christermj/bachelor-2026-3d-printing-underwater-prototyping/figurer/ekstra/20260315_124856.jpg

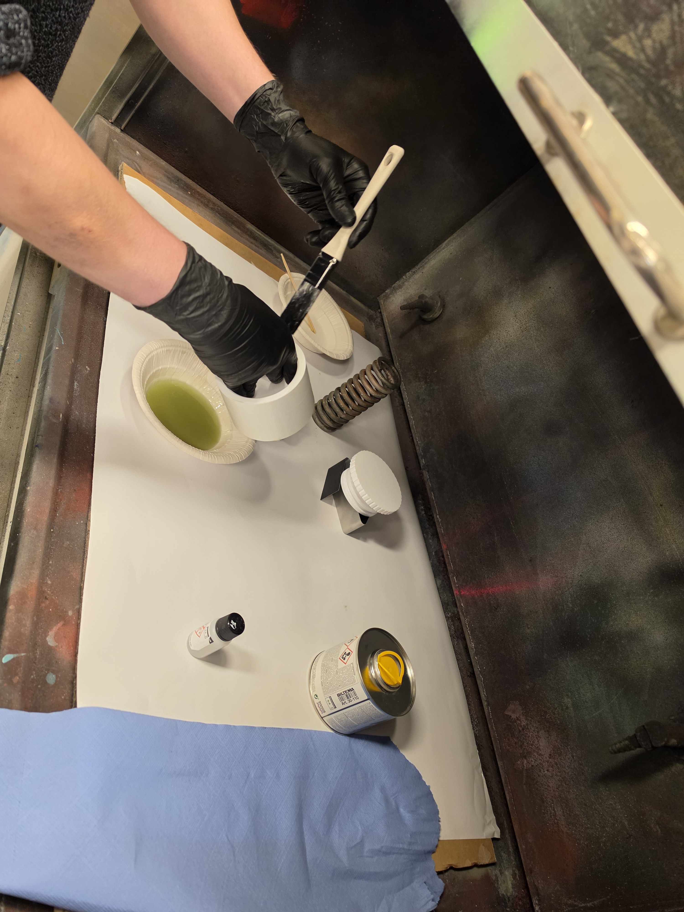
figurer/ekstra/20260315_124856.jpg
