christermj/bachelor-2026-3d-printing-underwater-prototyping/figurer/ekstra/IMG20260116104449.jpg

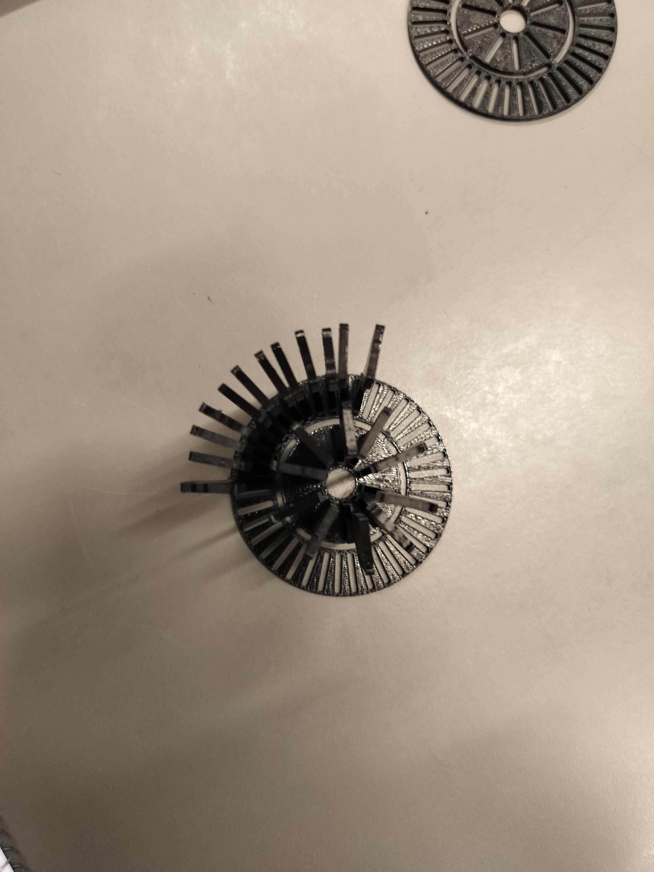
figurer/ekstra/IMG20260116104449.jpg
