christermj/bachelor-2026-3d-printing-underwater-prototyping/figurer/ekstra/IMG20260116105501.jpg

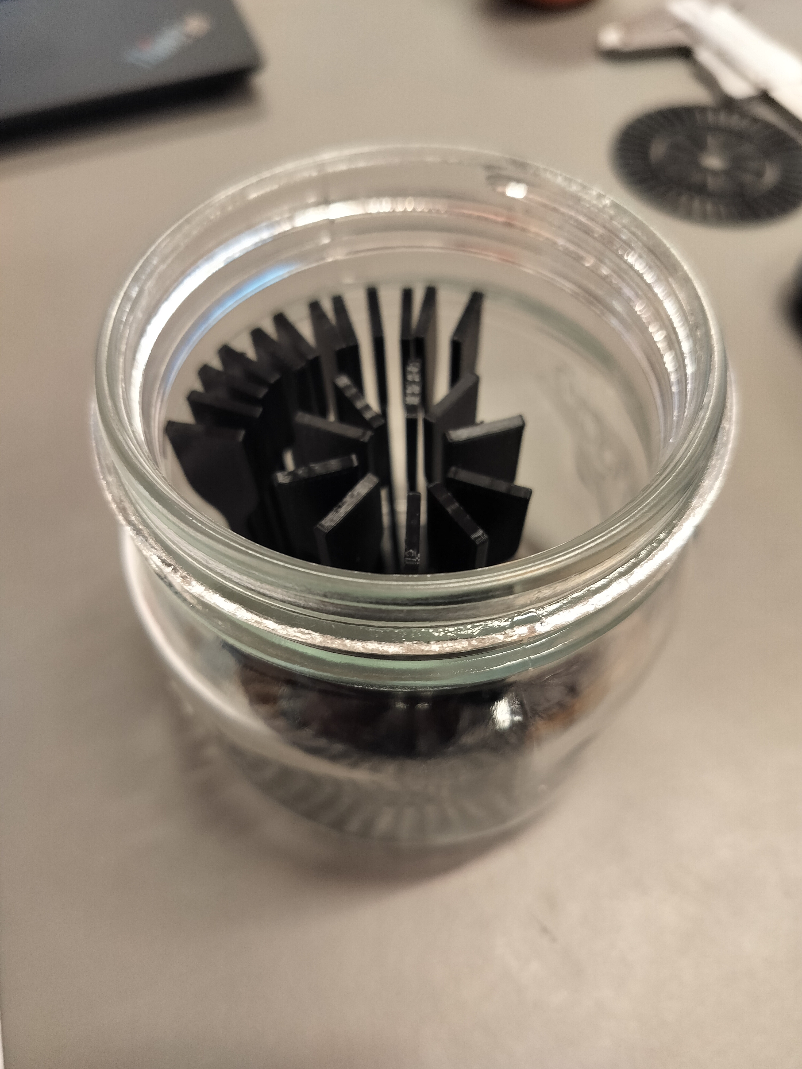
figurer/ekstra/IMG20260116105501.jpg
