christermj/bachelor-2026-3d-printing-underwater-prototyping/figurer/ekstra/IMG20260117135606.jpg

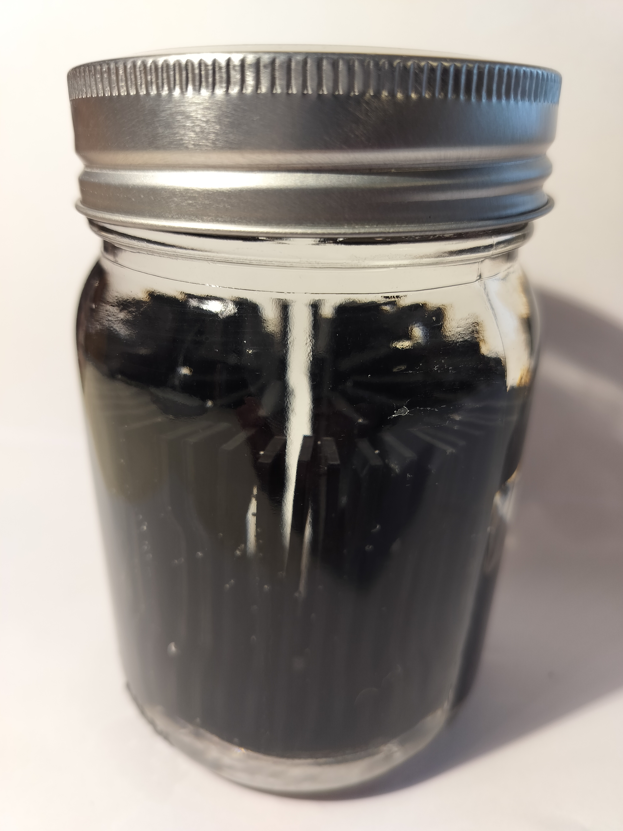
figurer/ekstra/IMG20260117135606.jpg
