christermj/bachelor-2026-3d-printing-underwater-prototyping/figurer/ekstra/IMG20260119151800.jpg

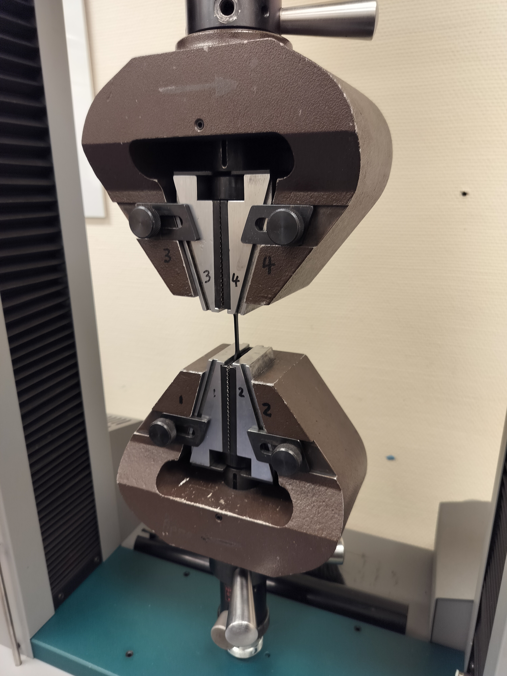
figurer/ekstra/IMG20260119151800.jpg
