christermj/bachelor-2026-3d-printing-underwater-prototyping/figurer/ekstra/IMG20260121113844.jpg

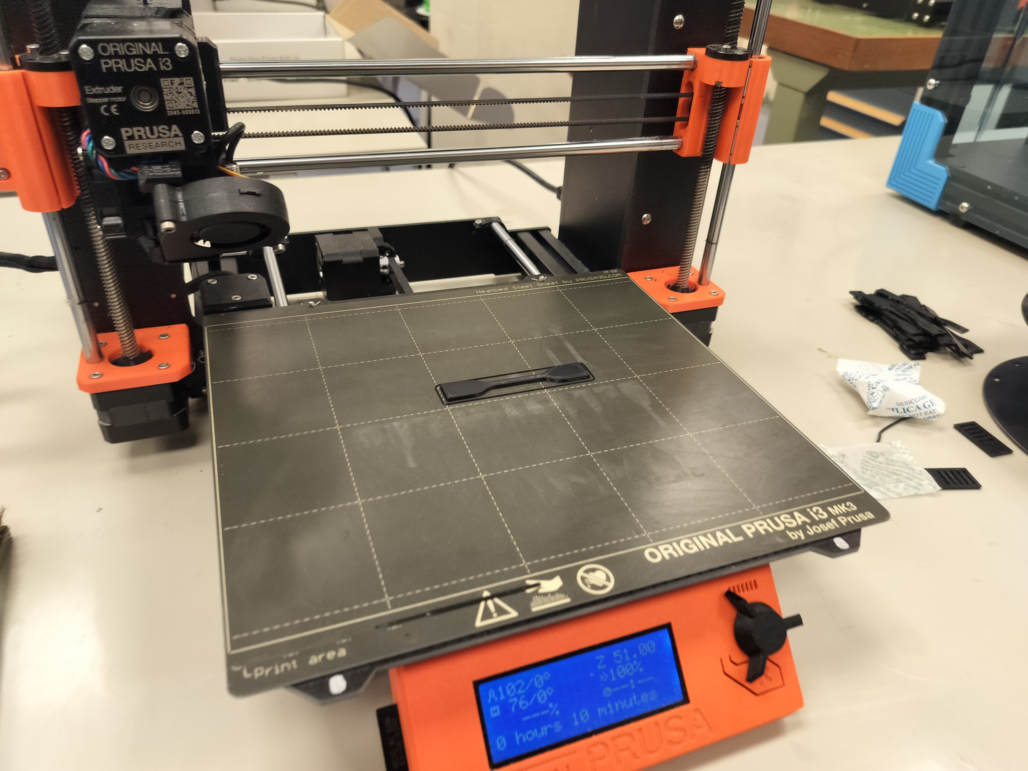
figurer/ekstra/IMG20260121113844.jpg
