christermj/bachelor-2026-3d-printing-underwater-prototyping/figurer/ekstra/IMG20260121113847.jpg

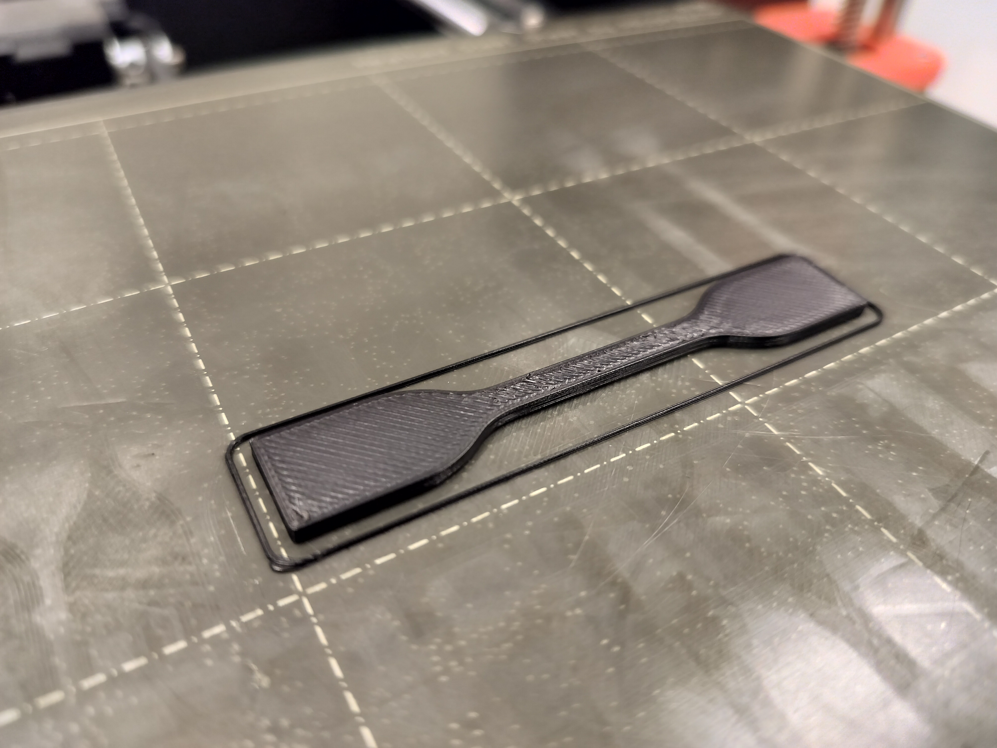
figurer/ekstra/IMG20260121113847.jpg
