christermj/bachelor-2026-3d-printing-underwater-prototyping/figurer/ekstra/IMG20260121144522.jpg

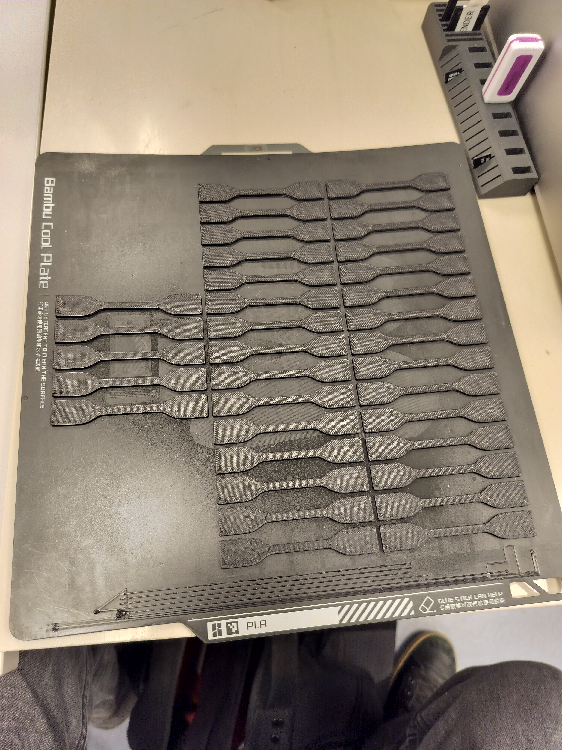
figurer/ekstra/IMG20260121144522.jpg
