christermj/bachelor-2026-3d-printing-underwater-prototyping/figurer/ekstra/IMG20260123111922.jpg

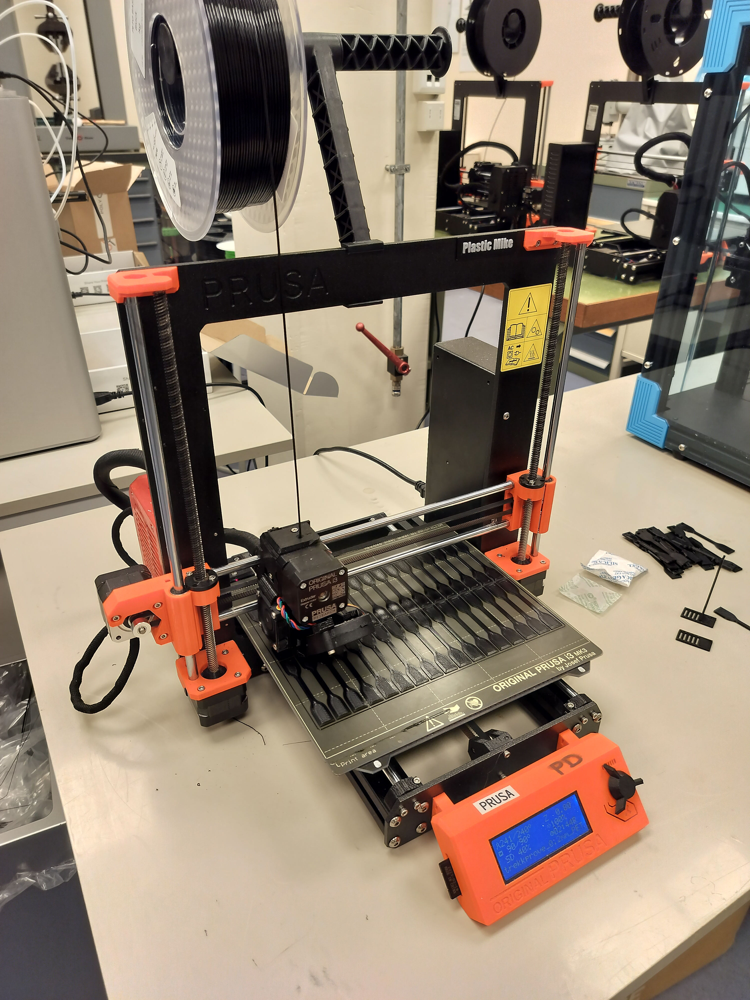
figurer/ekstra/IMG20260123111922.jpg
