christermj/bachelor-2026-3d-printing-underwater-prototyping/figurer/ekstra/IMG20260124142021.jpg

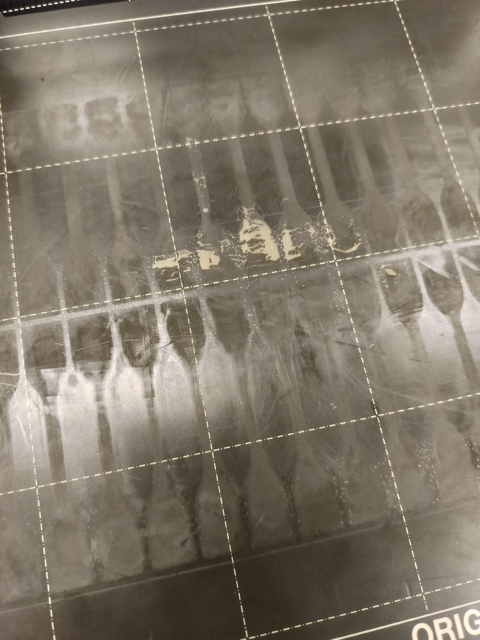
figurer/ekstra/IMG20260124142021.jpg
