christermj/bachelor-2026-3d-printing-underwater-prototyping/figurer/ekstra/IMG20260124142024.jpg

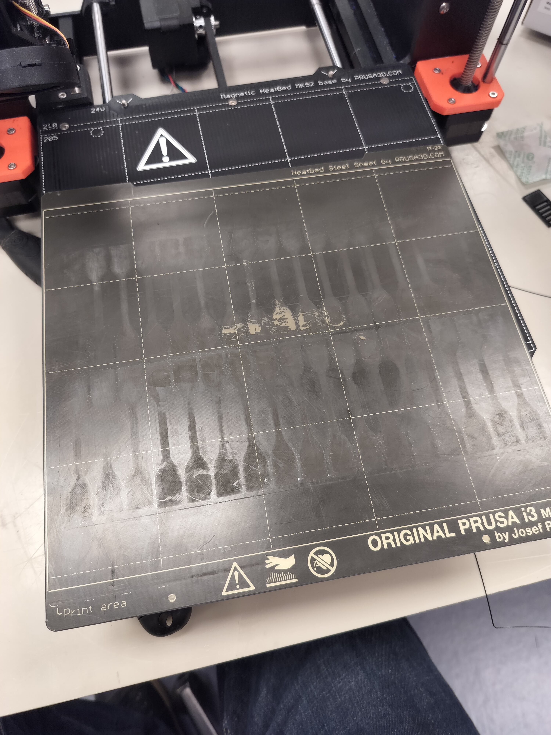
figurer/ekstra/IMG20260124142024.jpg
