christermj/bachelor-2026-3d-printing-underwater-prototyping/figurer/ekstra/IMG20260126114533.jpg

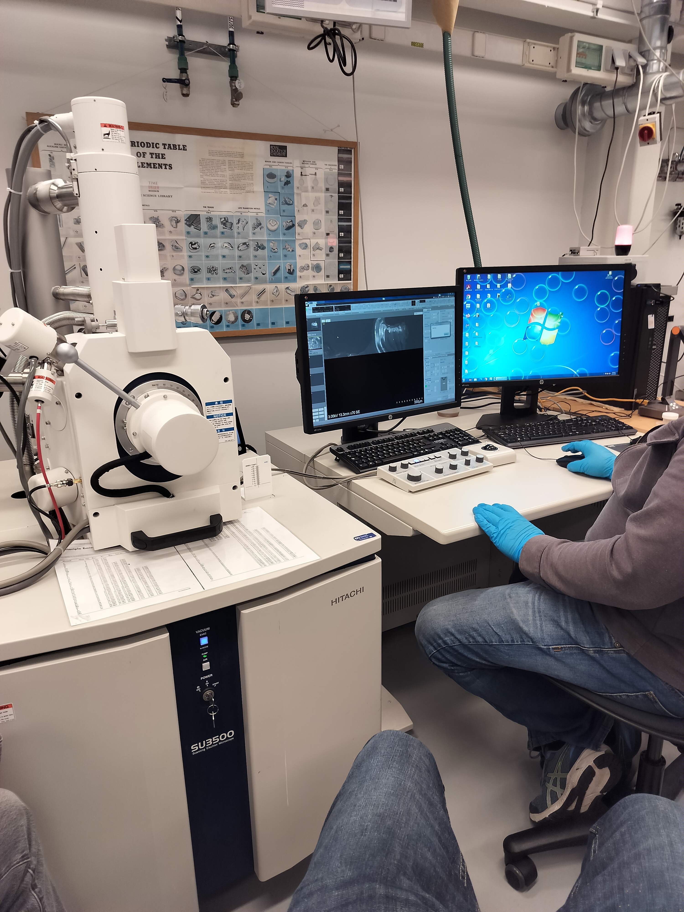
figurer/ekstra/IMG20260126114533.jpg
