christermj/bachelor-2026-3d-printing-underwater-prototyping/figurer/ekstra/IMG20260127100453.jpg

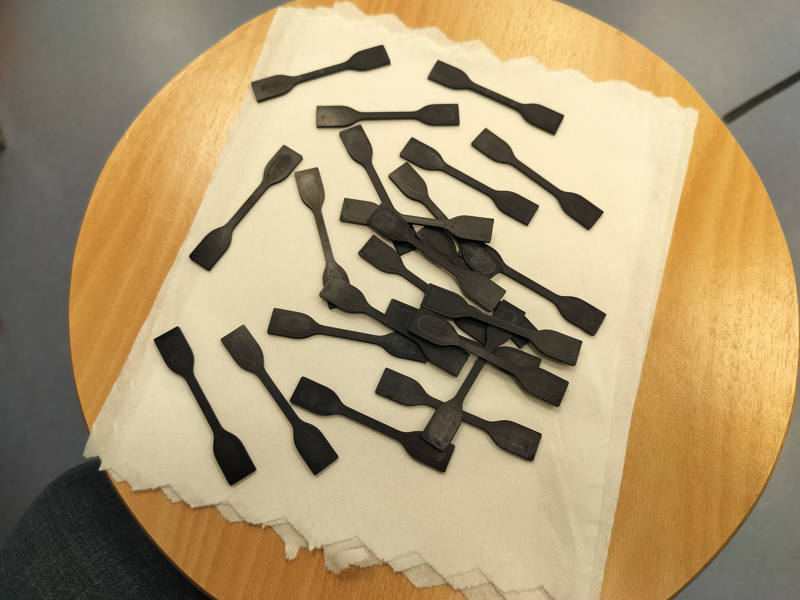
figurer/ekstra/IMG20260127100453.jpg
