christermj/bachelor-2026-3d-printing-underwater-prototyping/figurer/ekstra/IMG20260128120439.jpg

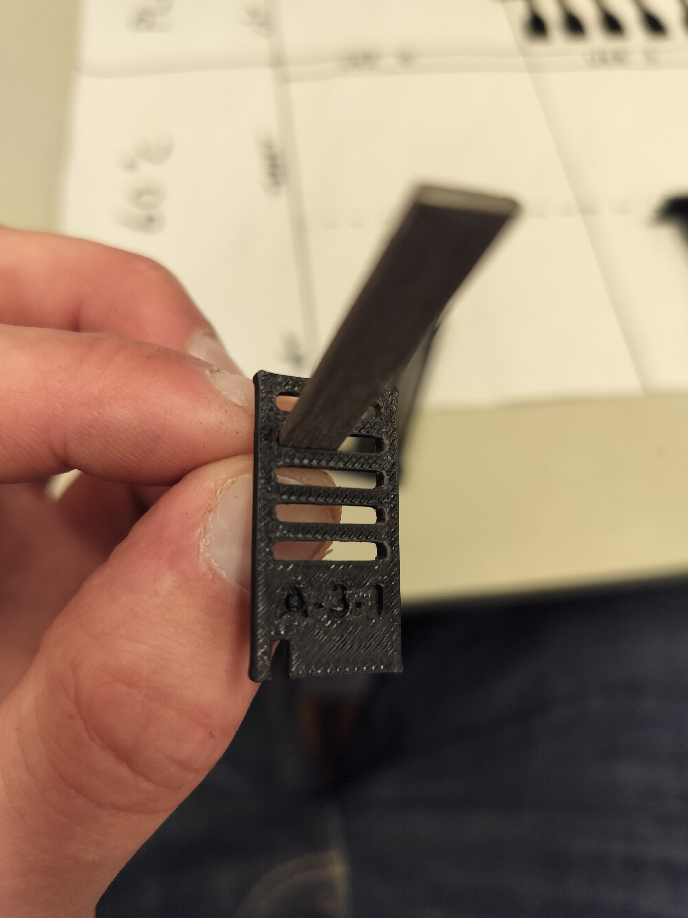
figurer/ekstra/IMG20260128120439.jpg
