christermj/bachelor-2026-3d-printing-underwater-prototyping/figurer/ekstra/IMG20260128121231.jpg

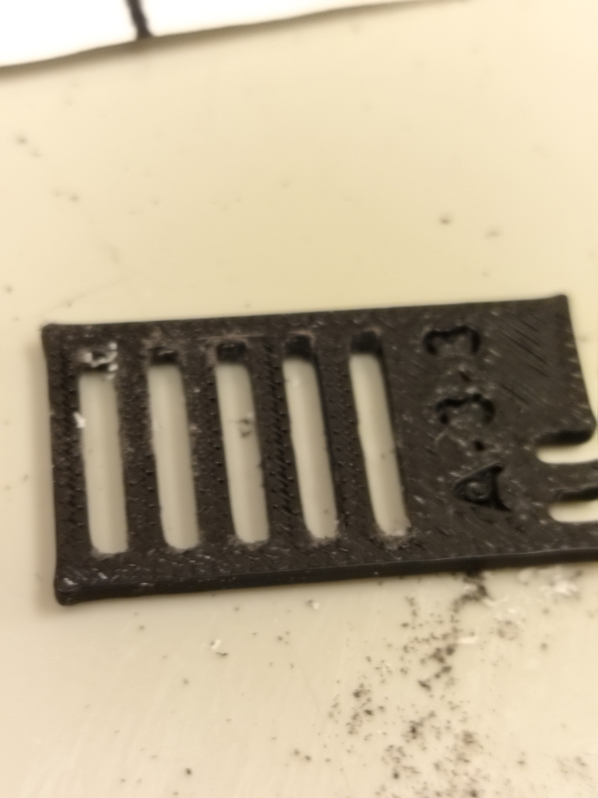
figurer/ekstra/IMG20260128121231.jpg
