christermj/bachelor-2026-3d-printing-underwater-prototyping/figurer/ekstra/IMG20260128122355.jpg

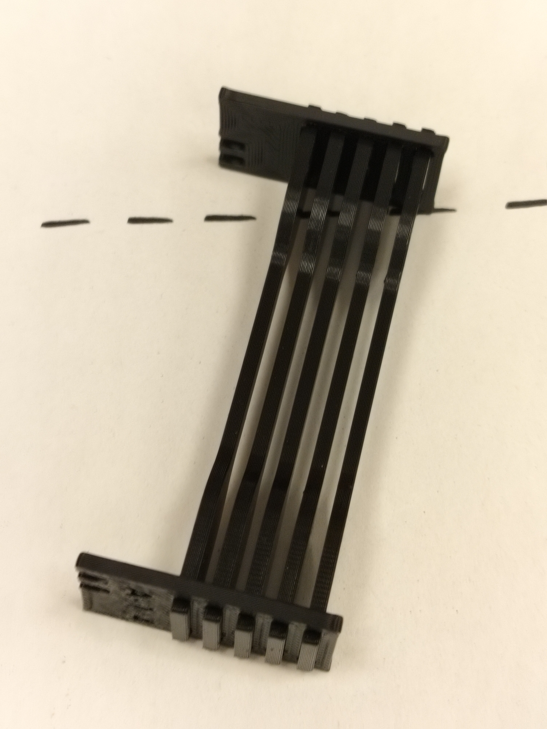
figurer/ekstra/IMG20260128122355.jpg
