christermj/bachelor-2026-3d-printing-underwater-prototyping/figurer/ekstra/Mikroskopering 17.jpeg

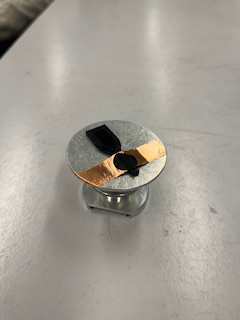
figurer/ekstra/Mikroskopering 17.jpeg
