christermj/bachelor-2026-3d-printing-underwater-prototyping/figurer/ekstra/oversikt strekkprøver.jpeg

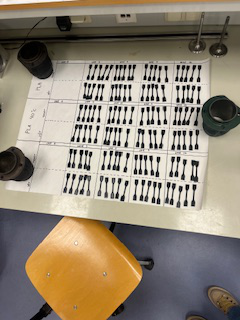
figurer/ekstra/oversikt strekkprøver.jpeg
