christermj/bachelor-2026-3d-printing-underwater-prototyping/figurer/ekstra/varmeskap_28.01.jpeg

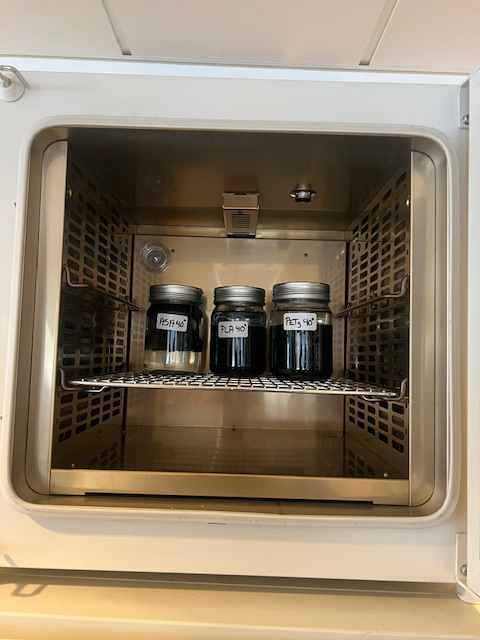
figurer/ekstra/varmeskap_28.01.jpeg
