christermj/bachelor-2026-3d-printing-underwater-prototyping/figurer/mikroskopi/001_0015.jpg

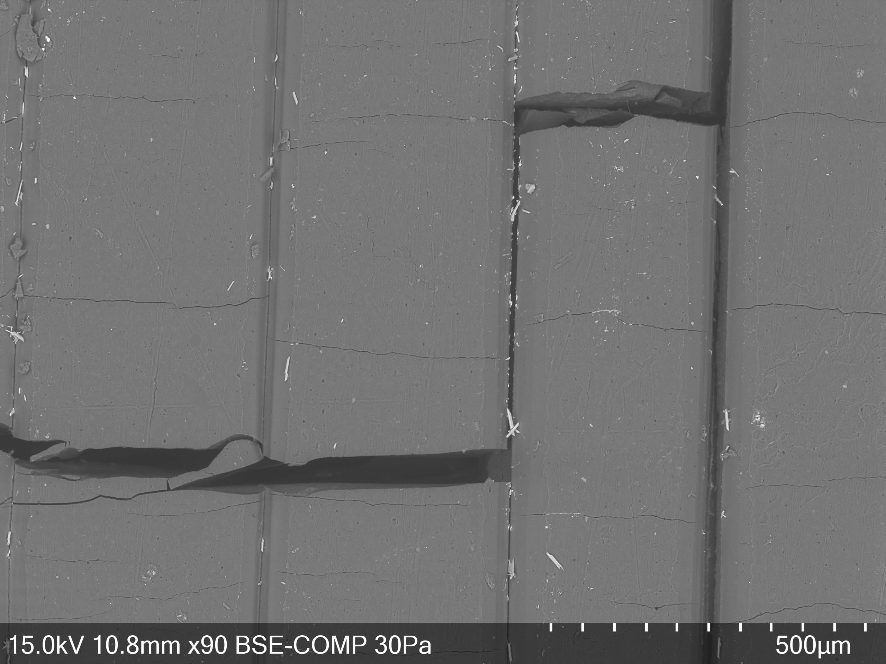
figurer/mikroskopi/001_0015.jpg
