christermj/bachelor-2026-3d-printing-underwater-prototyping/figurer/mikroskopi/116963_ASA_000002.jpg

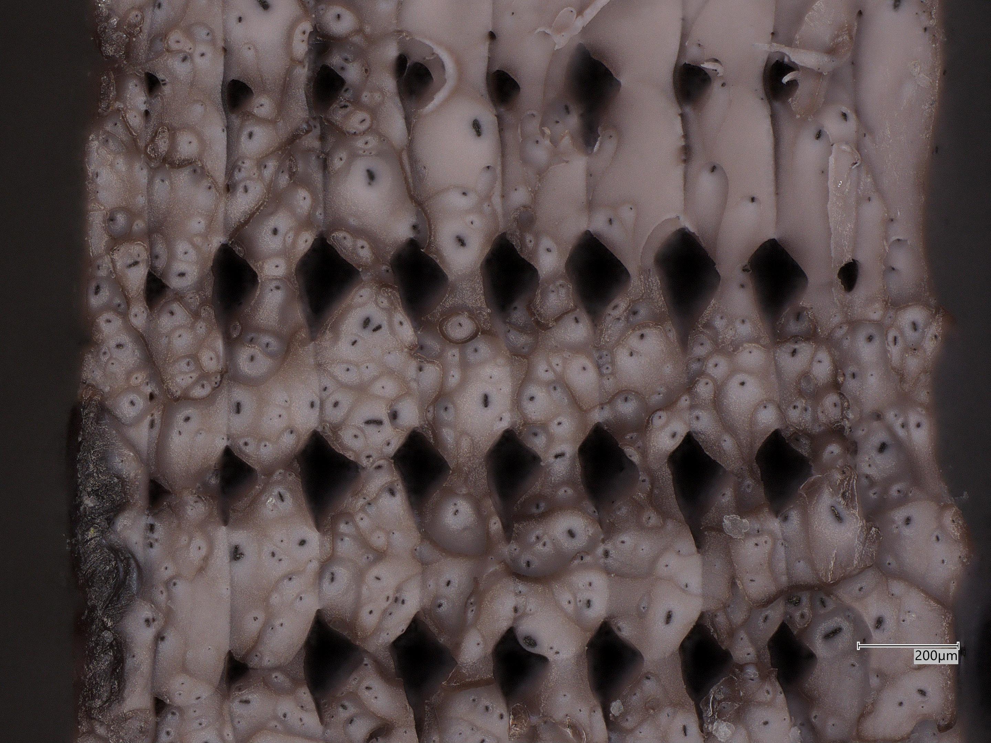
figurer/mikroskopi/116963_ASA_000002.jpg
