christermj/bachelor-2026-3d-printing-underwater-prototyping/figurer/mikroskopi/116963_PETG_000001.jpg

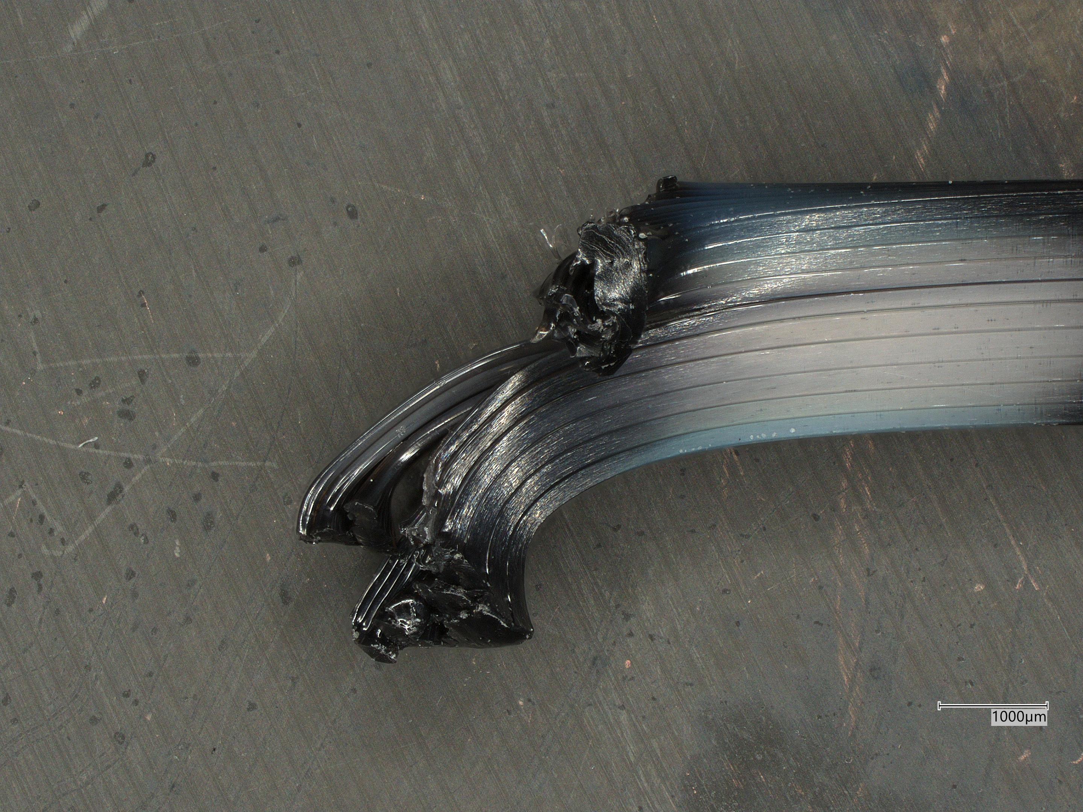
figurer/mikroskopi/116963_PETG_000001.jpg
