christermj/bachelor-2026-3d-printing-underwater-prototyping/figurer/mikroskopi/116963_PLA_000000.jpg

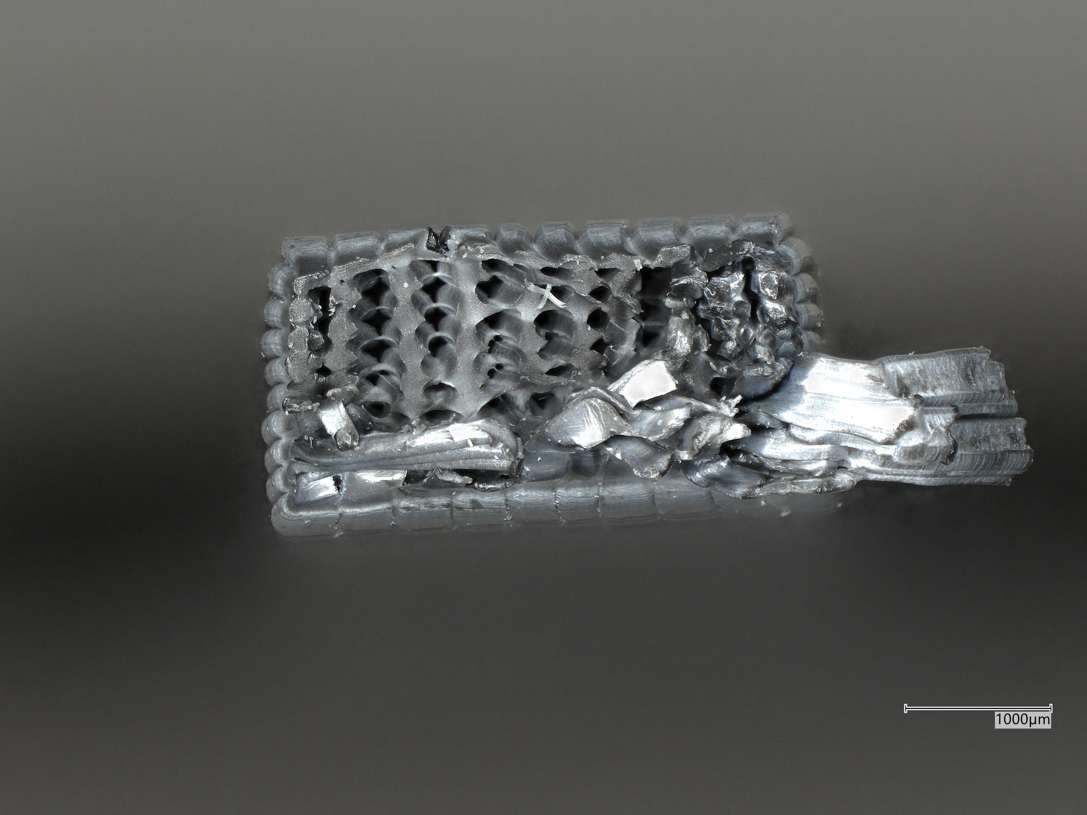
figurer/mikroskopi/116963_PLA_000000.jpg
