christermj/bachelor-2026-3d-printing-underwater-prototyping/figurer/mikroskopi/ASA 011.jpg

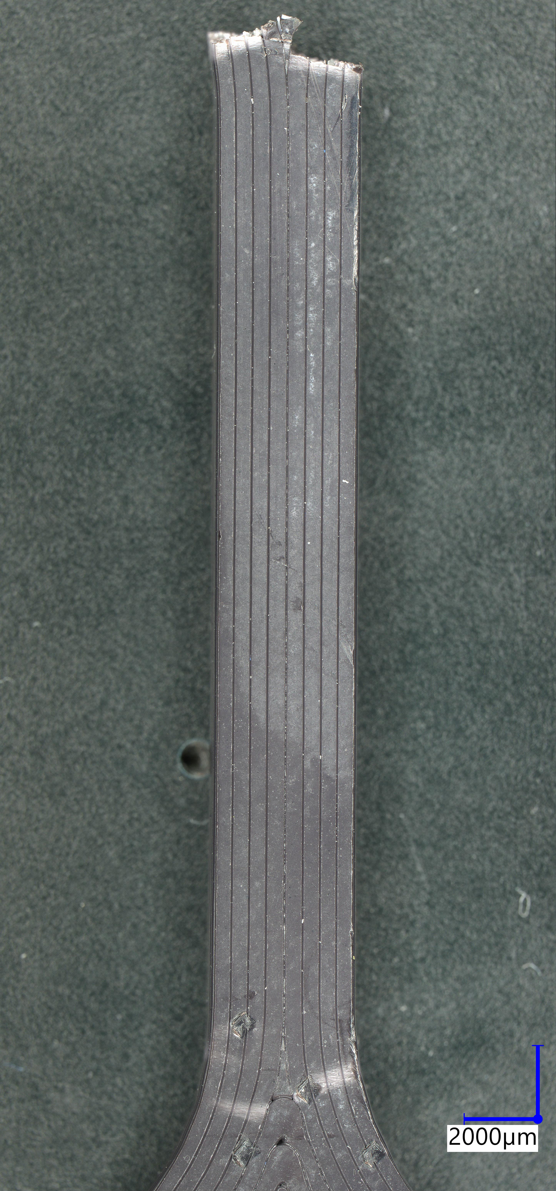
figurer/mikroskopi/ASA 011.jpg
