christermj/bachelor-2026-3d-printing-underwater-prototyping/figurer/mikroskopi/ASA 012.jpg

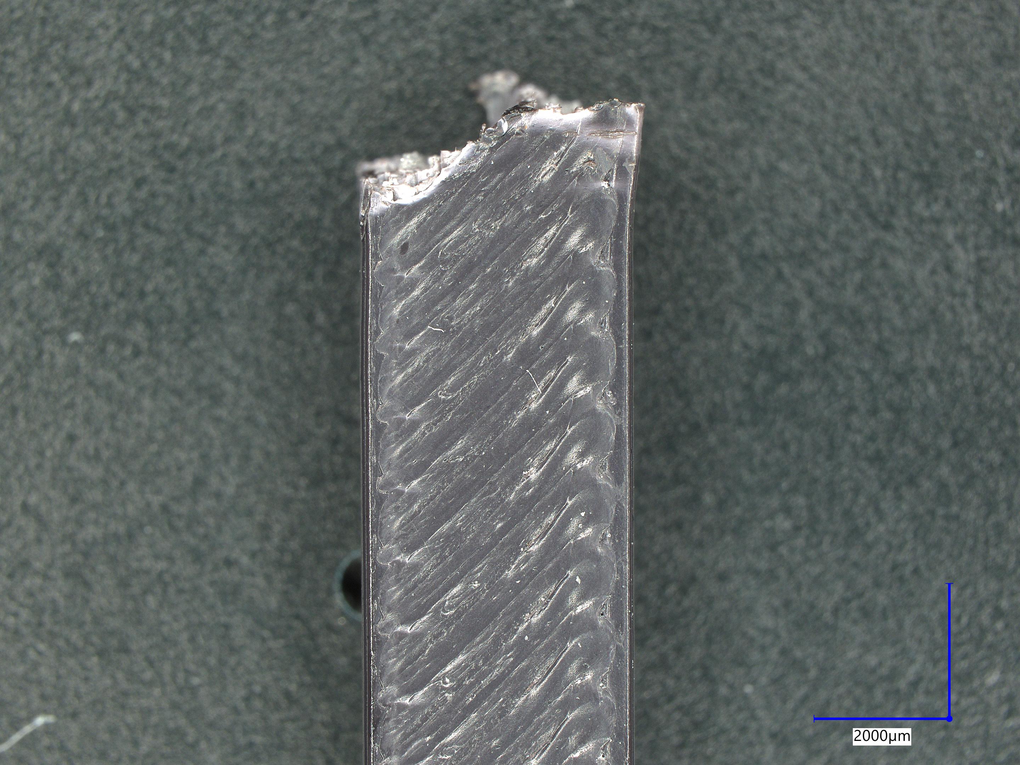
figurer/mikroskopi/ASA 012.jpg
