christermj/bachelor-2026-3d-printing-underwater-prototyping/figurer/mikroskopi/C_1_1_1_b.jpg

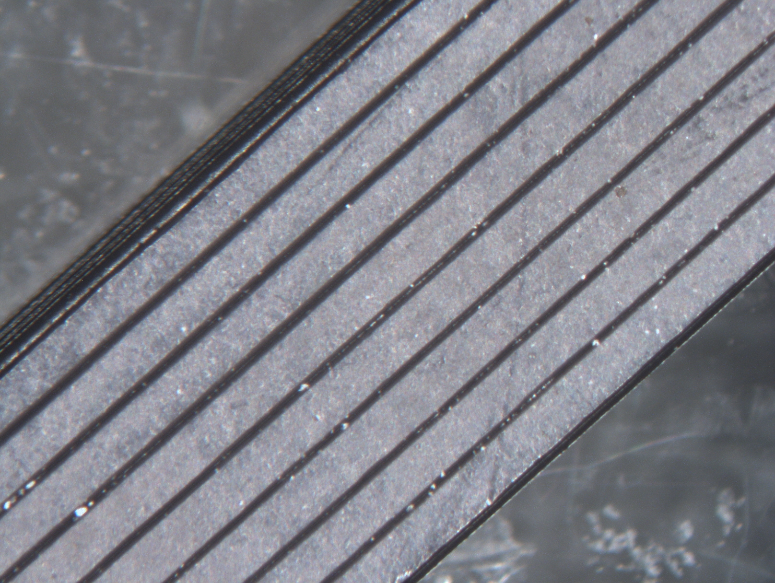
figurer/mikroskopi/C_1_1_1_b.jpg
