christermj/bachelor-2026-3d-printing-underwater-prototyping/figurer/mikroskopi/C_1_1_1_d.jpg

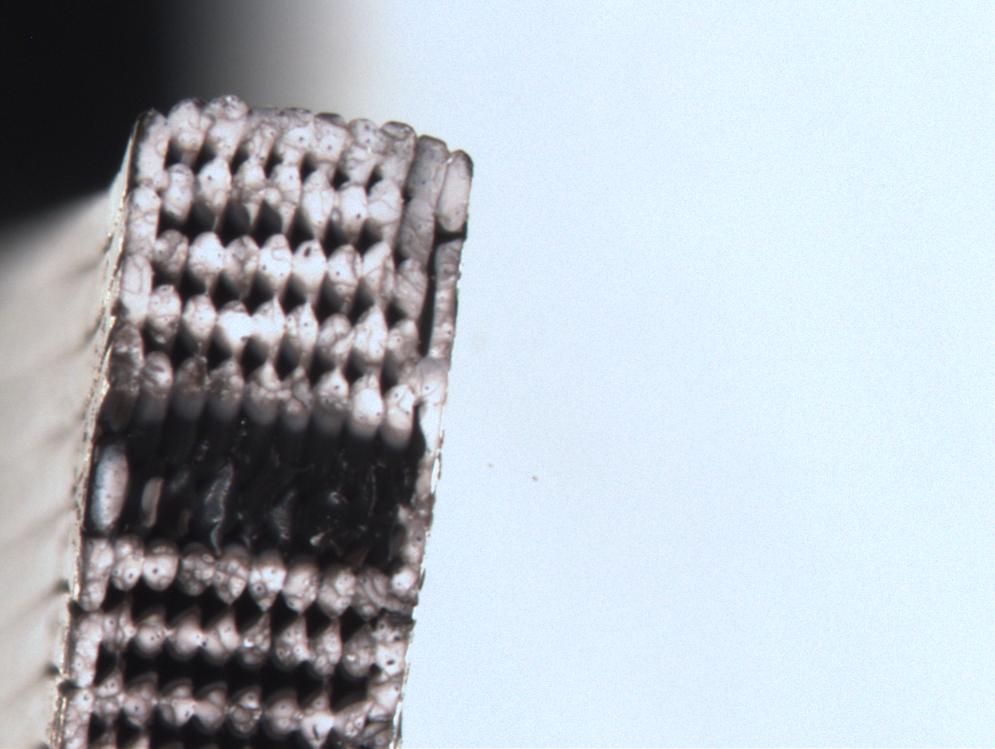
figurer/mikroskopi/C_1_1_1_d.jpg
