christermj/bachelor-2026-3d-printing-underwater-prototyping/figurer/mikroskopi/C_1_2_2_b.jpg

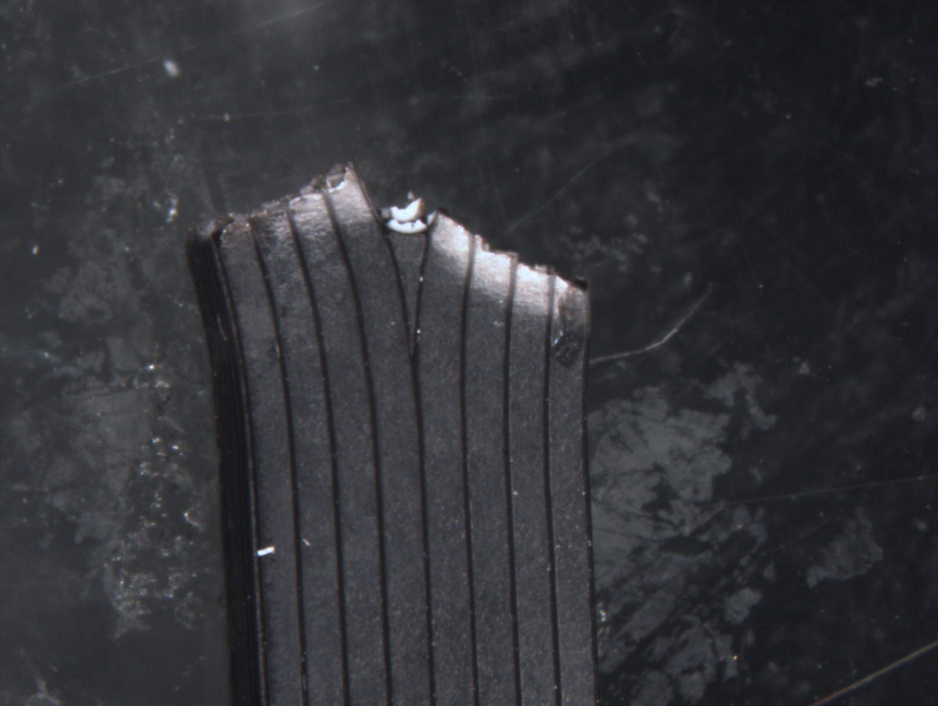
figurer/mikroskopi/C_1_2_2_b.jpg
