christermj/bachelor-2026-3d-printing-underwater-prototyping/figurer/mikroskopi/C_1_2_2_d.jpg

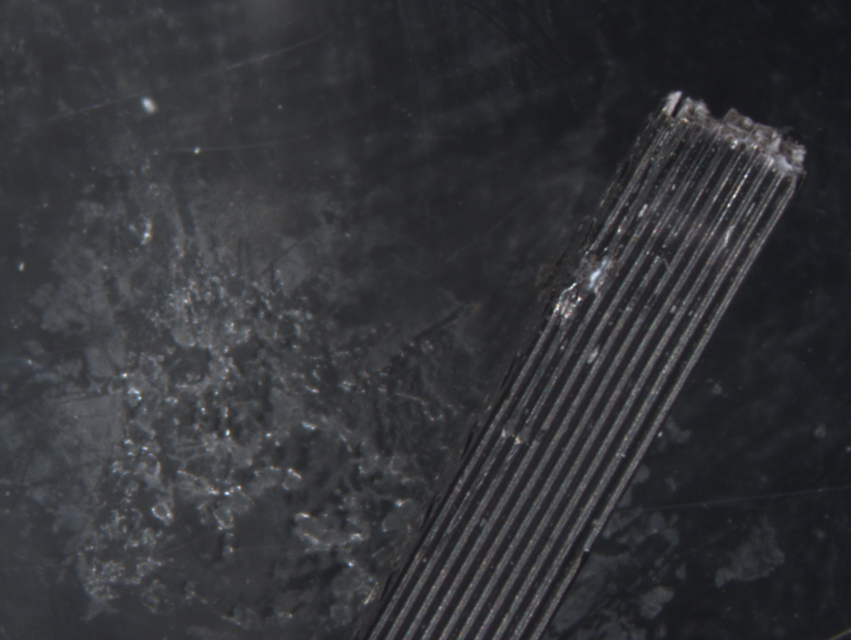
figurer/mikroskopi/C_1_2_2_d.jpg
