christermj/bachelor-2026-3d-printing-underwater-prototyping/figurer/mikroskopi/C_3_1_1_c.jpg

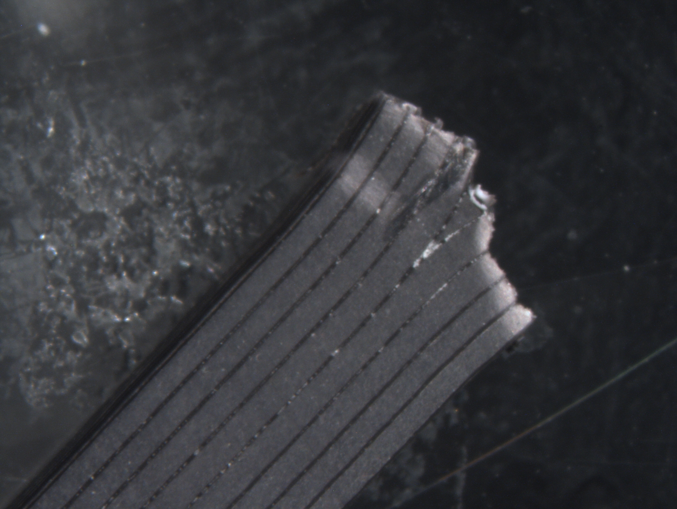
figurer/mikroskopi/C_3_1_1_c.jpg
