christermj/bachelor-2026-3d-printing-underwater-prototyping/figurer/mikroskopi/C_3_1_1_e.jpg

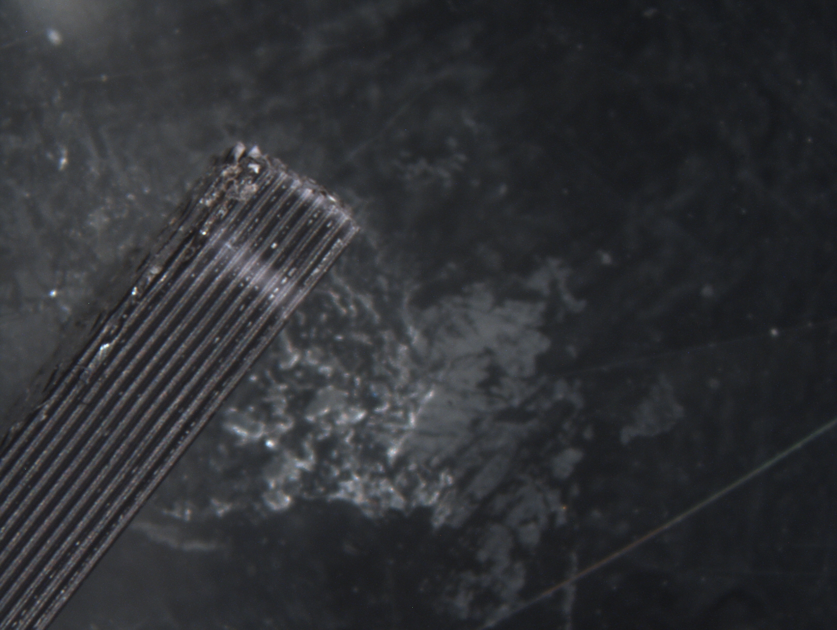
figurer/mikroskopi/C_3_1_1_e.jpg
