christermj/bachelor-2026-3d-printing-underwater-prototyping/figurer/mikroskopi/C_3_1_1_f.jpg

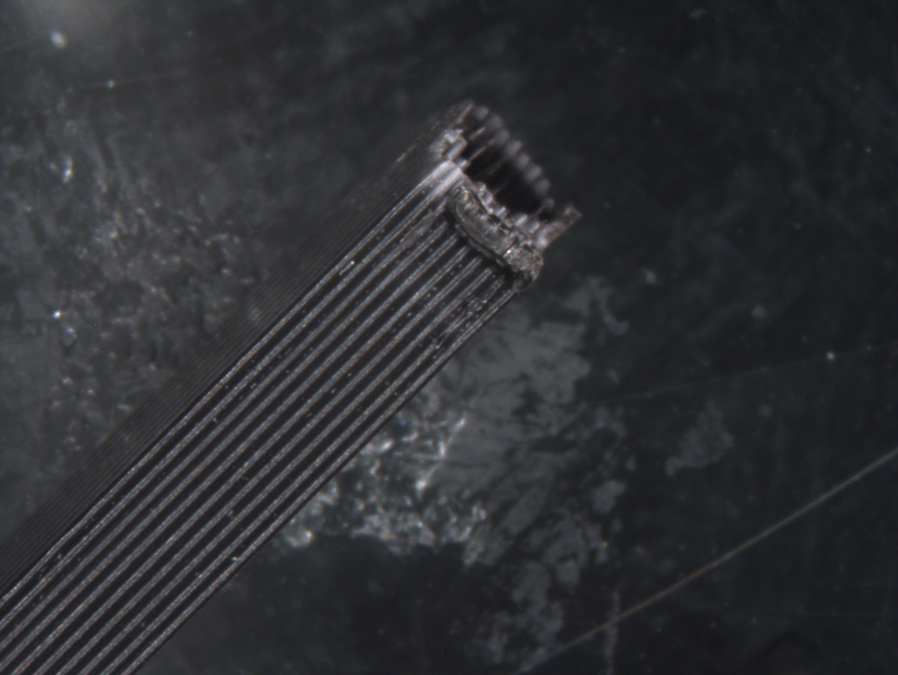
figurer/mikroskopi/C_3_1_1_f.jpg
