christermj/bachelor-2026-3d-printing-underwater-prototyping/figurer/mikroskopi/C_3_2_2_a.jpg

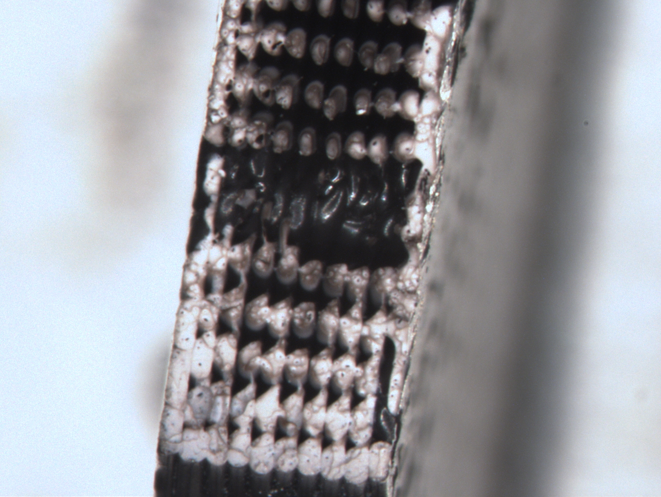
figurer/mikroskopi/C_3_2_2_a.jpg
