christermj/bachelor-2026-3d-printing-underwater-prototyping/figurer/mikroskopi/EDS 01.png

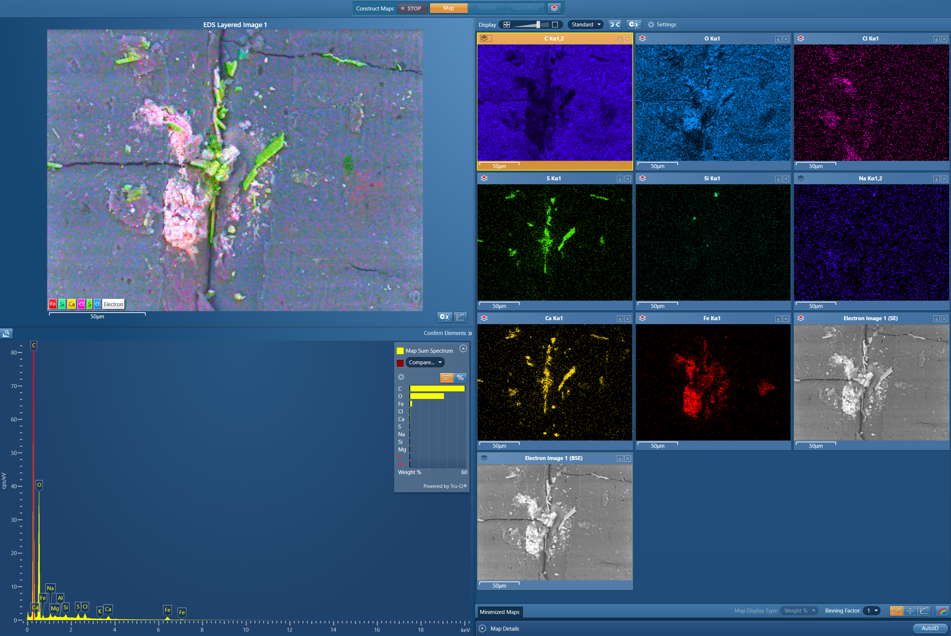
figurer/mikroskopi/EDS 01.png
