christermj/bachelor-2026-3d-printing-underwater-prototyping/figurer/mikroskopi/EDS 03.png

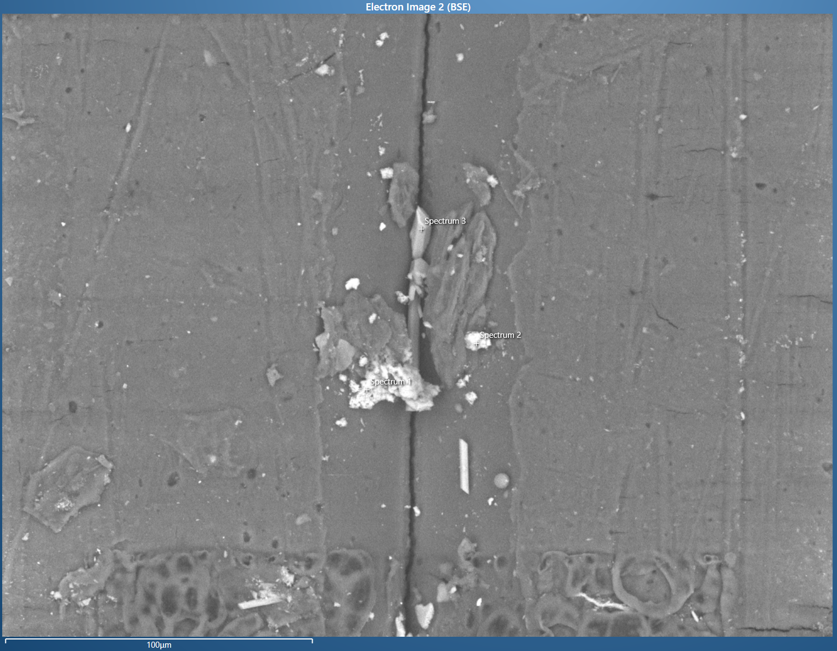
figurer/mikroskopi/EDS 03.png
