christermj/bachelor-2026-3d-printing-underwater-prototyping/figurer/mikroskopi/Image-7ASA.jpg

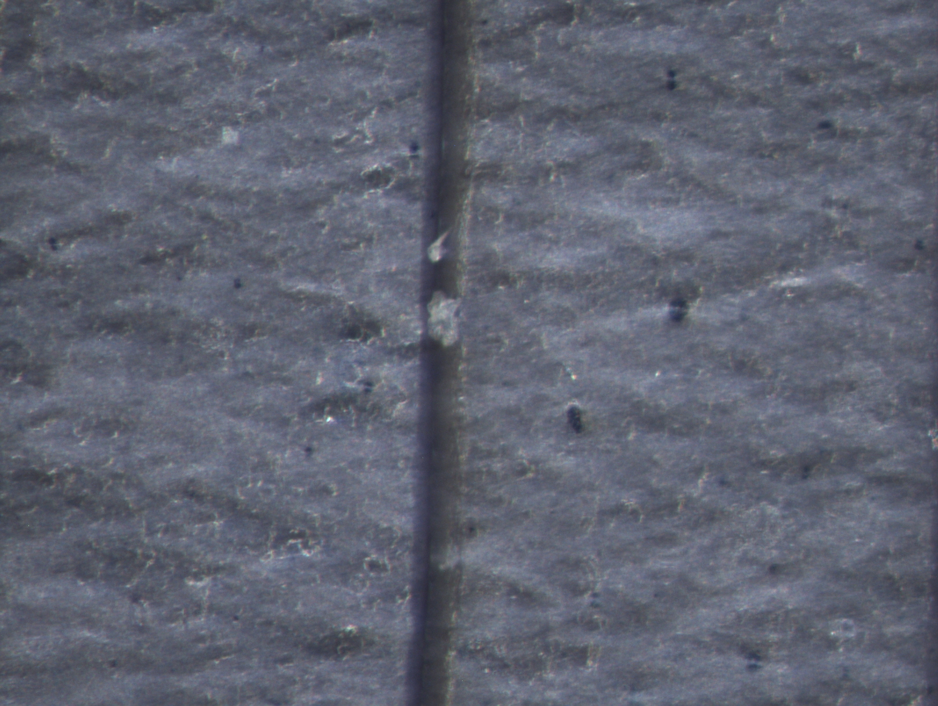
figurer/mikroskopi/Image-7ASA.jpg
