christermj/bachelor-2026-3d-printing-underwater-prototyping/figurer/mikroskopi/Image-15.jpg

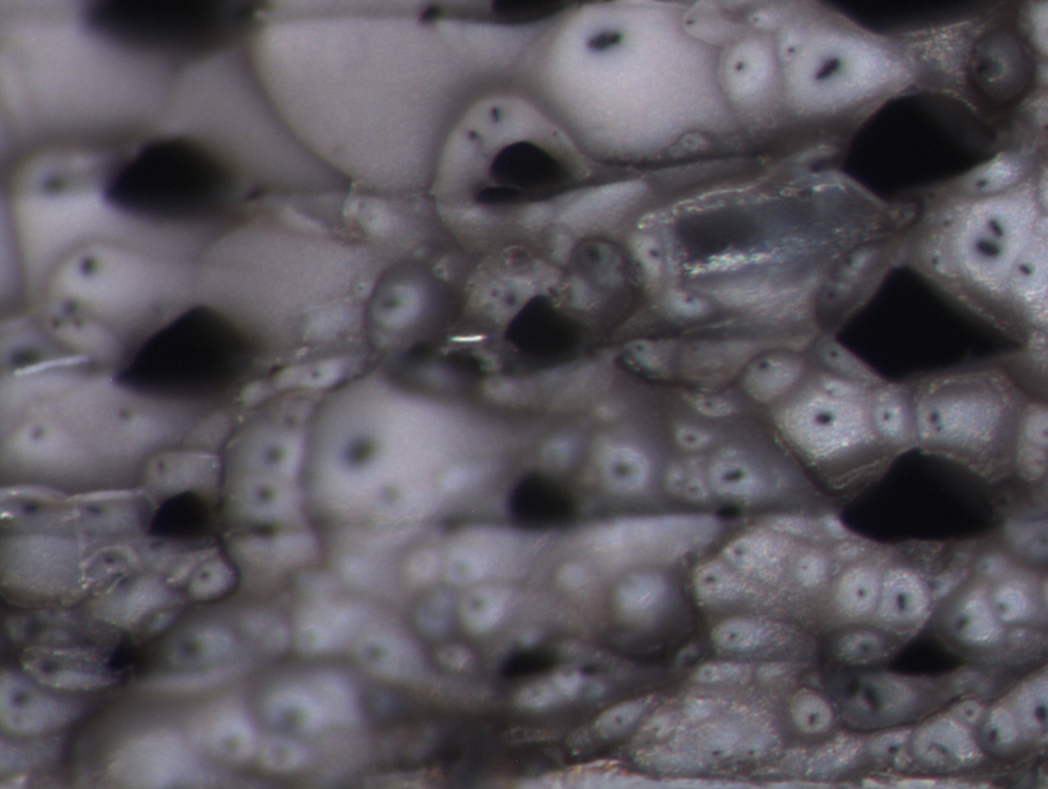
figurer/mikroskopi/Image-15.jpg
