christermj/bachelor-2026-3d-printing-underwater-prototyping/figurer/mikroskopi/Image-19.jpg

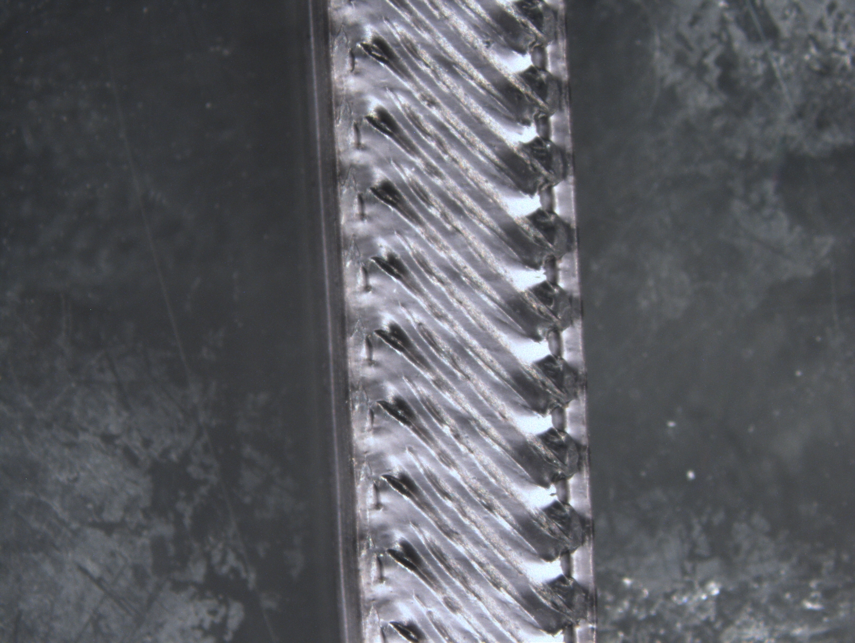
figurer/mikroskopi/Image-19.jpg
