christermj/bachelor-2026-3d-printing-underwater-prototyping/figurer/mikroskopi/Image-20.jpg

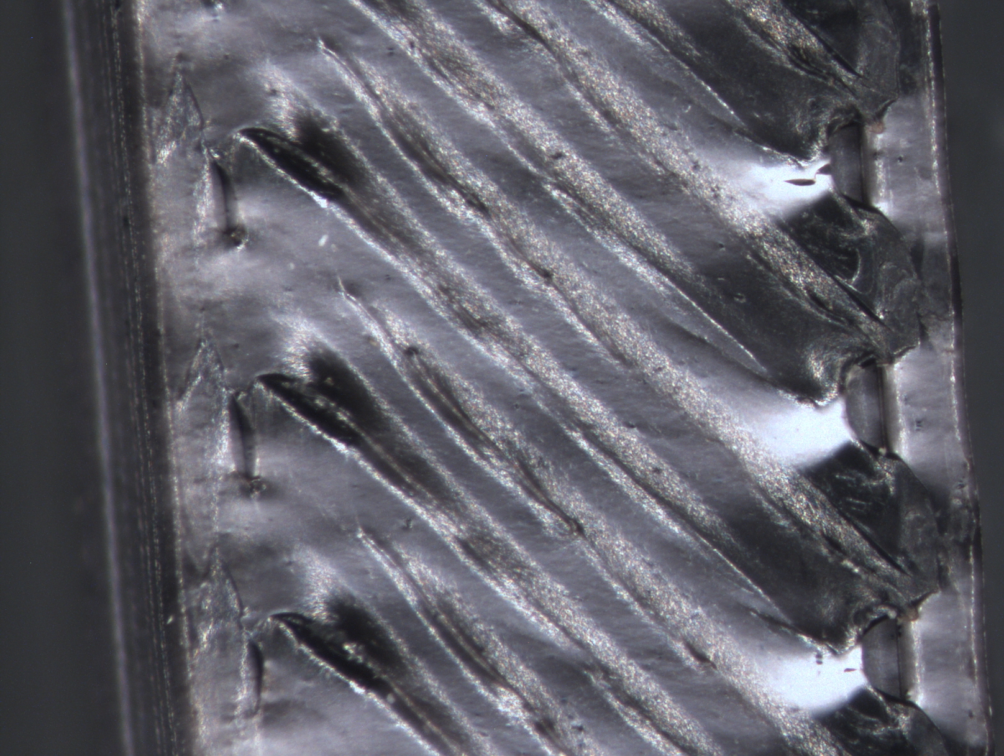
figurer/mikroskopi/Image-20.jpg
