christermj/bachelor-2026-3d-printing-underwater-prototyping/figurer/mikroskopi/Image-23.jpg

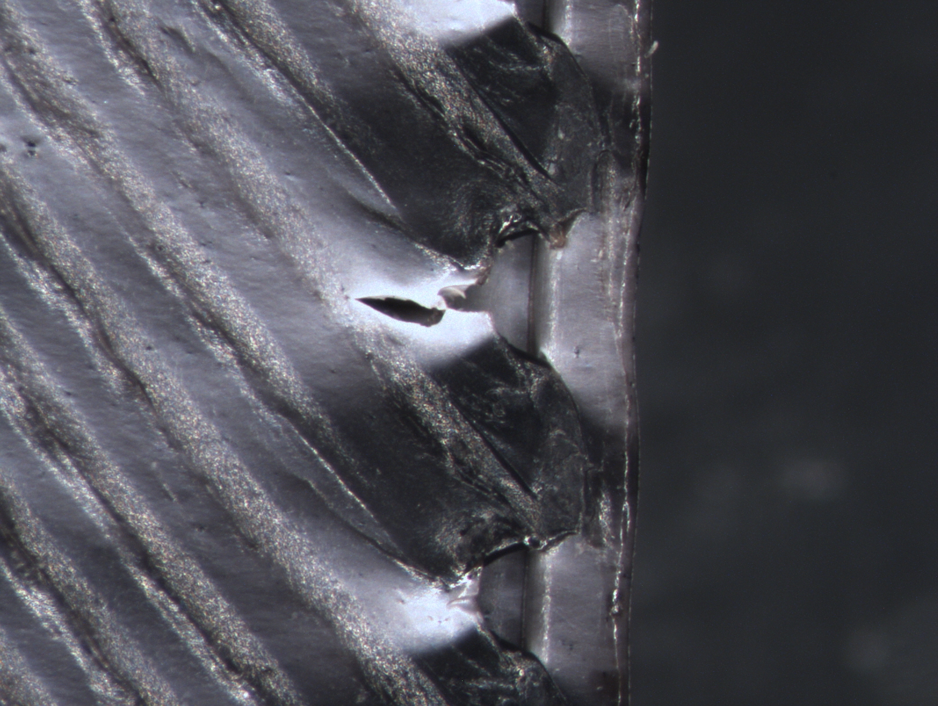
figurer/mikroskopi/Image-23.jpg
