christermj/bachelor-2026-3d-printing-underwater-prototyping/figurer/mikroskopi/Image-asa1.jpg

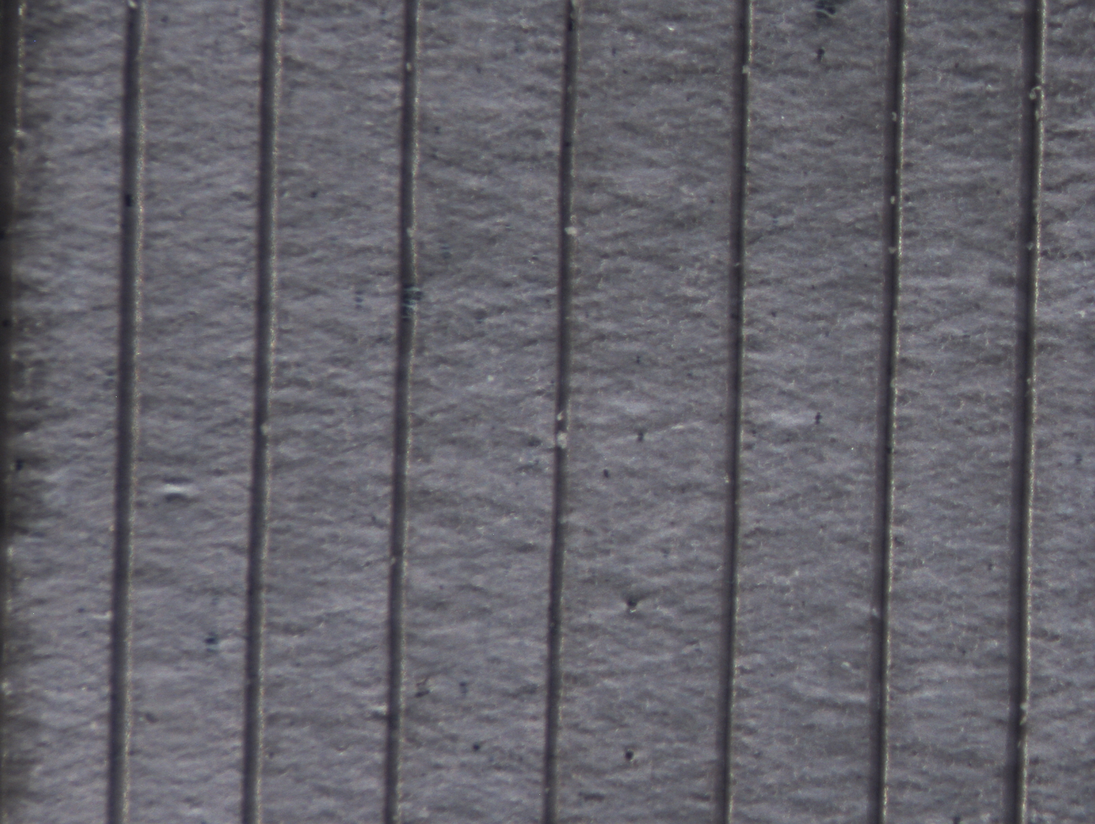
figurer/mikroskopi/Image-asa1.jpg
