christermj/bachelor-2026-3d-printing-underwater-prototyping/figurer/mikroskopi/PETG 015.jpg

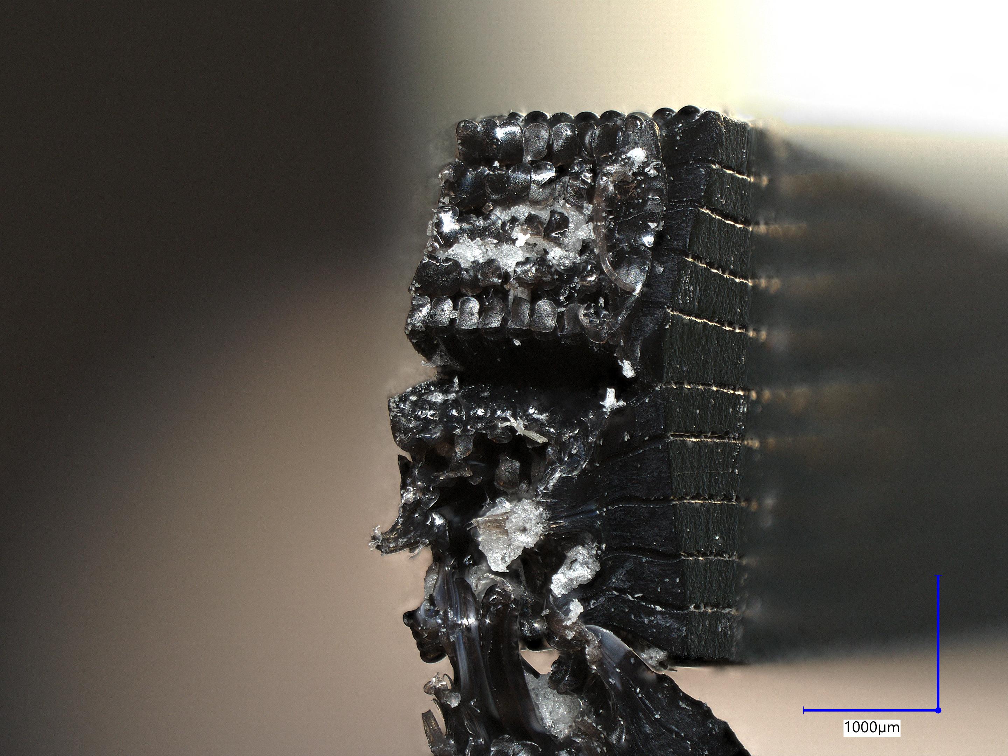
figurer/mikroskopi/PETG 015.jpg
