christermj/bachelor-2026-3d-printing-underwater-prototyping/figurer/mikroskopi/PETG 018.jpg

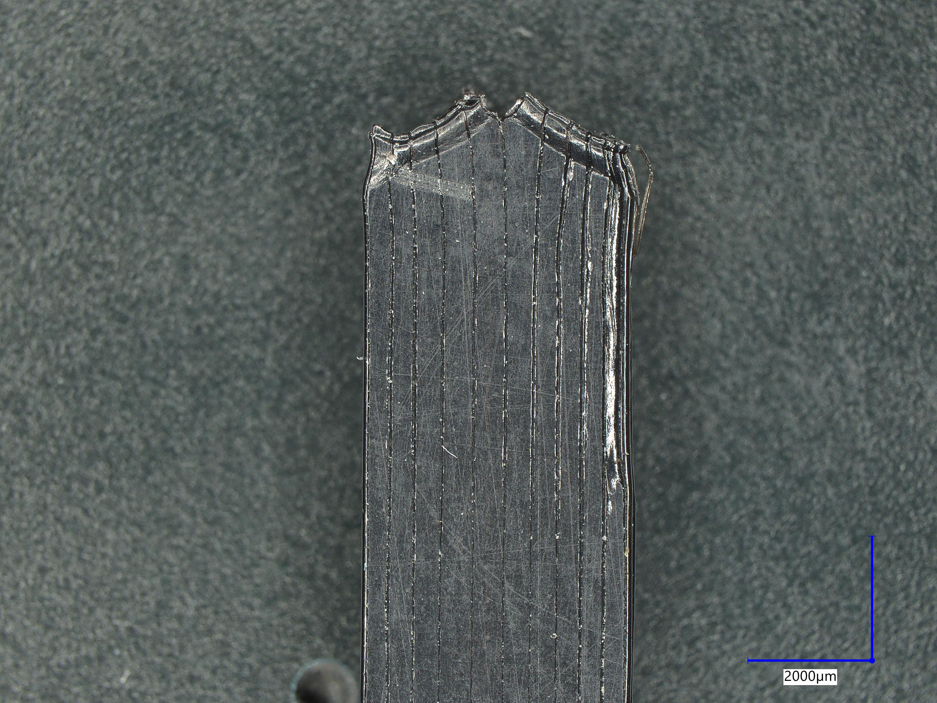
figurer/mikroskopi/PETG 018.jpg
