christermj/bachelor-2026-3d-printing-underwater-prototyping/figurer/mikroskopi/PETG 023.jpg

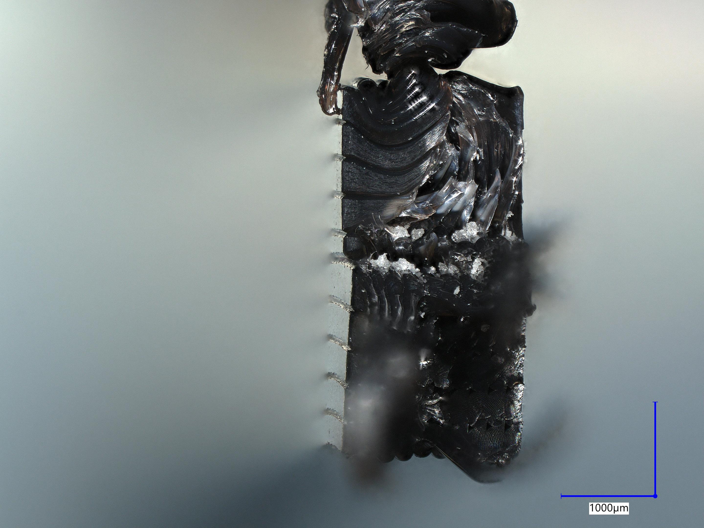
figurer/mikroskopi/PETG 023.jpg
