christermj/bachelor-2026-3d-printing-underwater-prototyping/figurer/mikroskopi/PETG 025.jpg

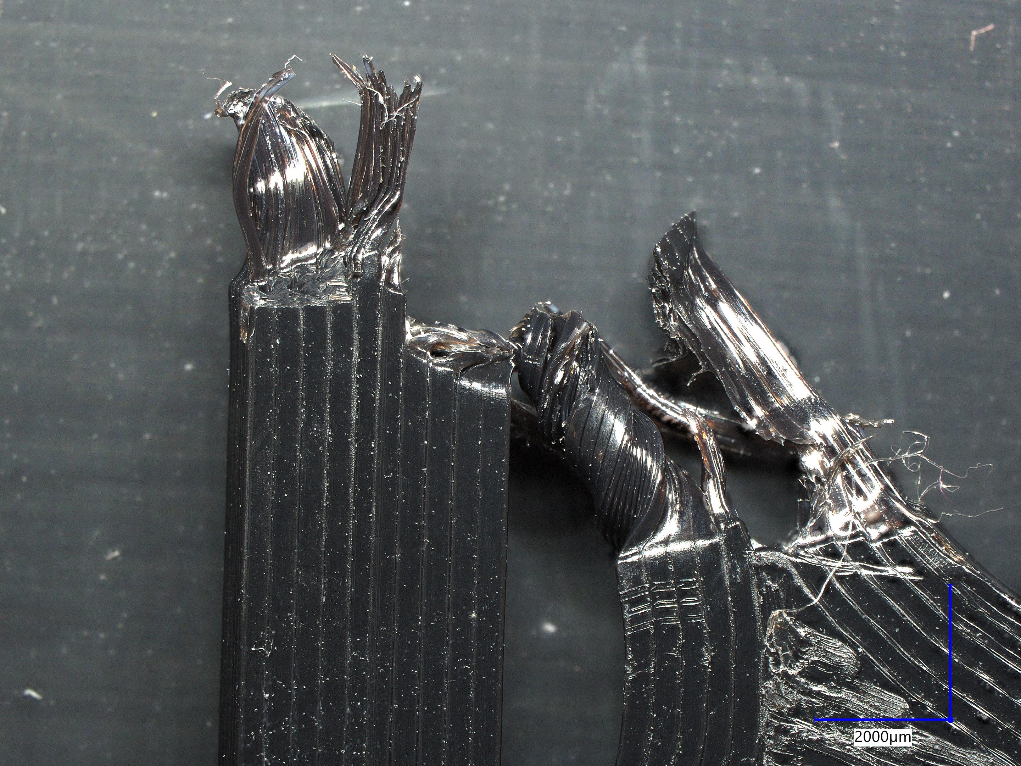
figurer/mikroskopi/PETG 025.jpg
