christermj/bachelor-2026-3d-printing-underwater-prototyping/figurer/mikroskopi/PETG 031.jpg

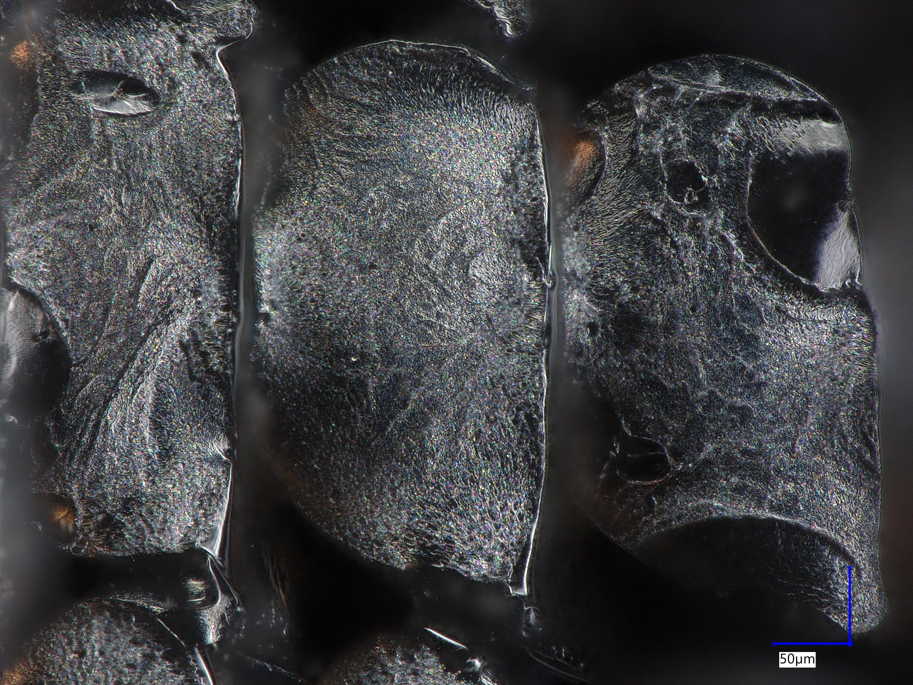
figurer/mikroskopi/PETG 031.jpg
