christermj/bachelor-2026-3d-printing-underwater-prototyping/figurer/mikroskopi/PLA 042.jpg

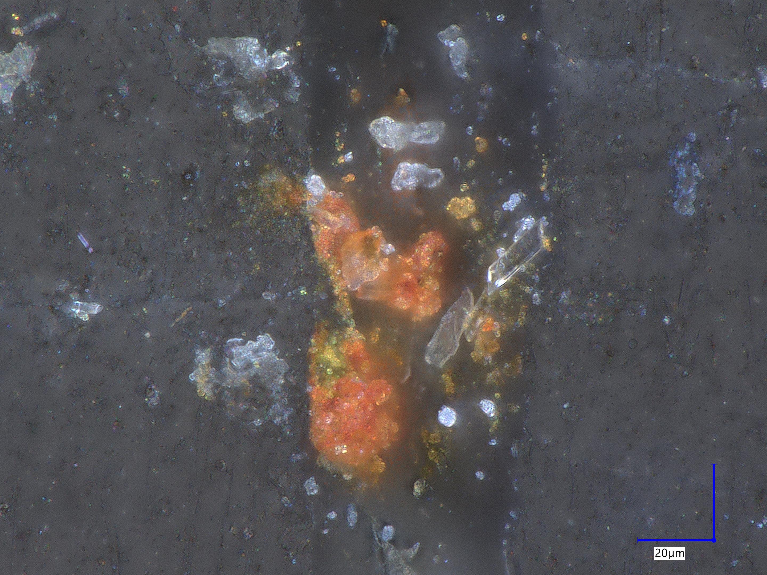
figurer/mikroskopi/PLA 042.jpg
