christermj/bachelor-2026-3d-printing-underwater-prototyping/cad/prototypekapsling/assy_klokke.SLDASM

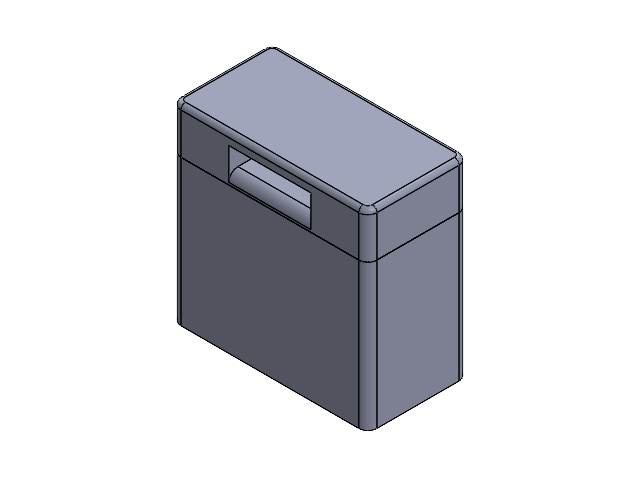
[picture p385: CAD file, 2026-05-21]
cad/prototypekapsling/assy_klokke.SLDASM
TMP102
lokk
